pepassaco/2m-PassBand/Simulaciones/1.jpg

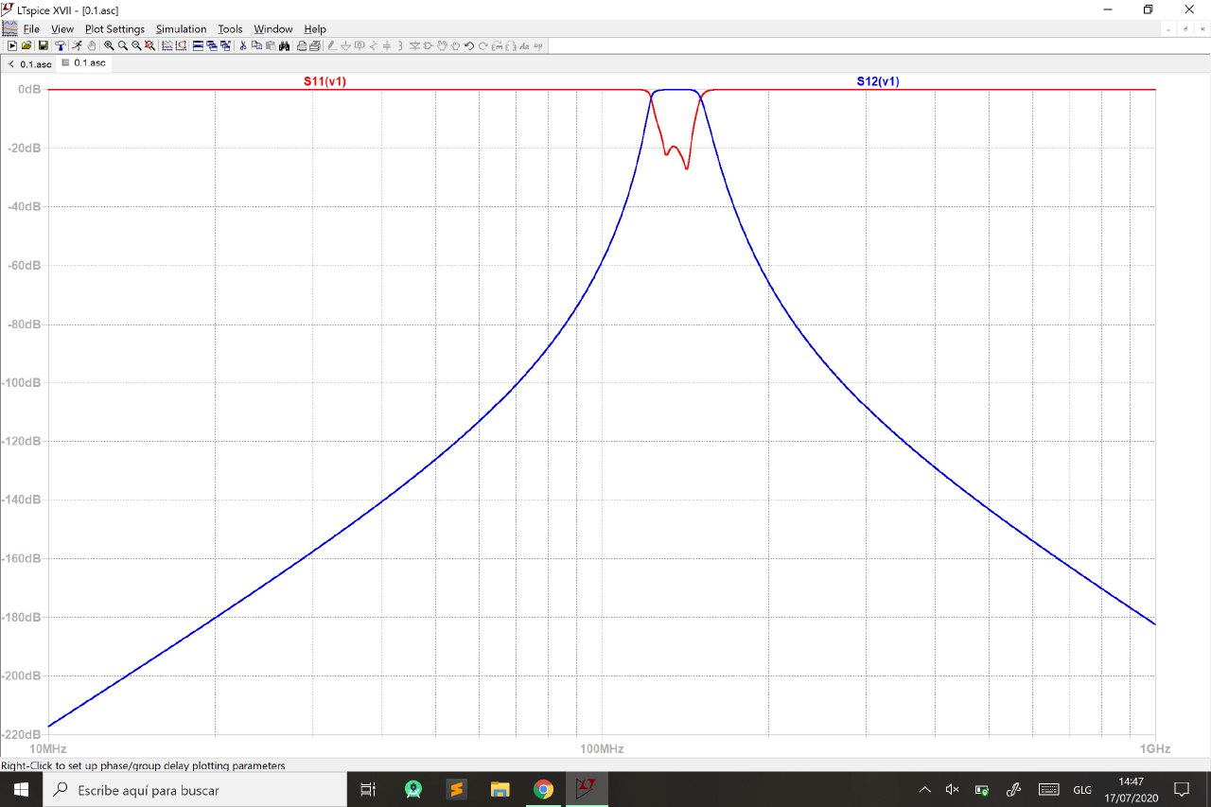
Simulaciones/1.jpg
