pepassaco/2m-PassBand/Simulaciones/3.jpg

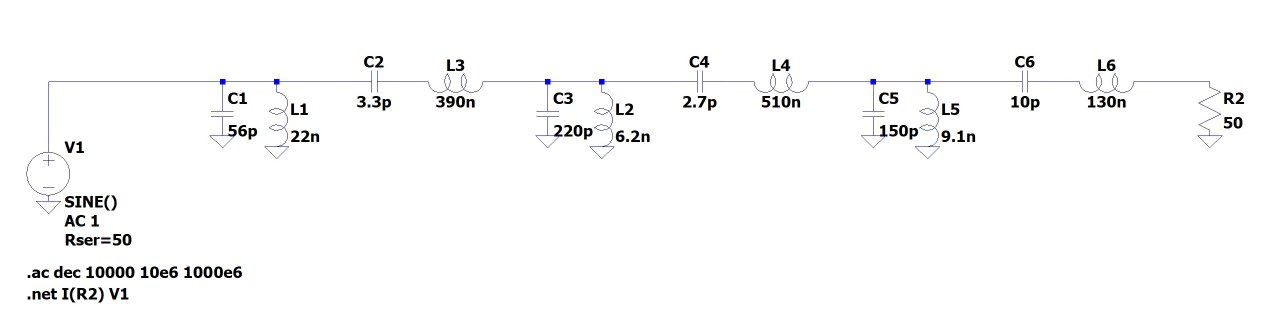
Simulaciones/3.jpg
