pepassaco/2m-PassBand/LTSpice/VHF-Passband.asc

C1: cap; 56p
C2: cap; 3.3p
C3: cap; 220p
C4: cap; 2.7p
C5: cap; 150p
C6: cap; 10p
L1: ind; 22n
L2: ind; 6.2n
L3: ind; 390n
L4: ind; 510n
L5: ind; 9.1n
L6: ind; 130n
R2: res; 50
V1: voltage; SINE(); AC 1; Rser=50
Named nets: 0
.ac dec 10000 10e6 1000e6
.net I(R2) V1
